mexomagno/TimerCharlas/Documentación/20131231_212455.jpg

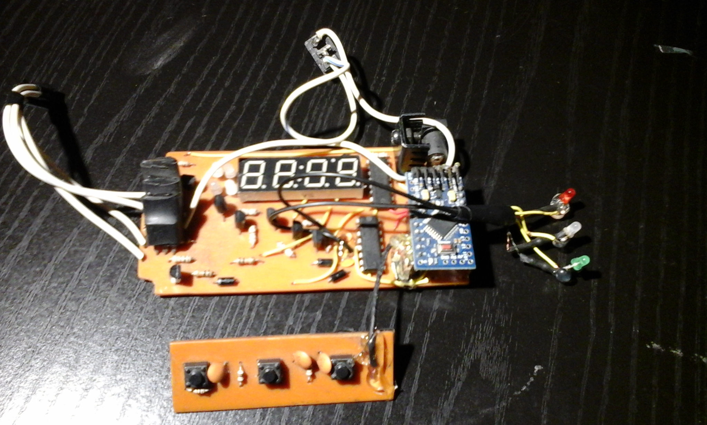
Documentación/20131231_212455.jpg
