mexomagno/TimerCharlas/Documentación/20131231_212502.jpg

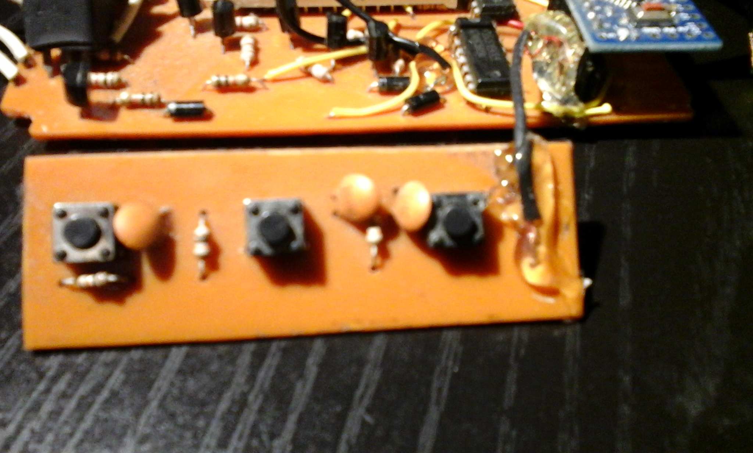
Documentación/20131231_212502.jpg
