mexomagno/TimerCharlas/Documentación/20131231_212513.jpg

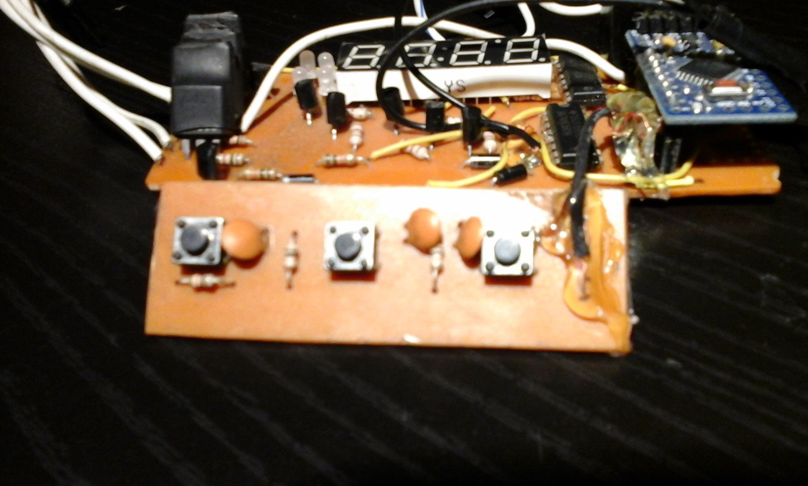
Documentación/20131231_212513.jpg
