mexomagno/TimerCharlas/Documentación/20131231_212531.jpg

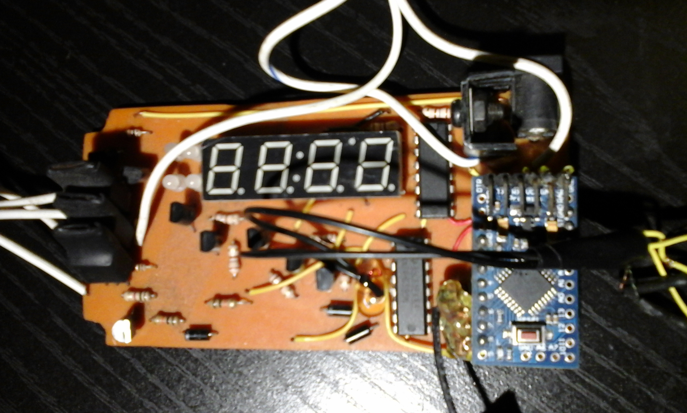
Documentación/20131231_212531.jpg
