mexomagno/TimerCharlas/Documentación/20131231_212555.jpg

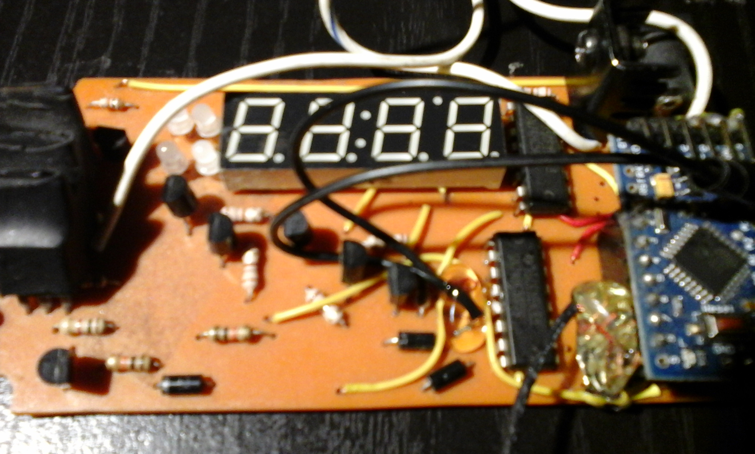
Documentación/20131231_212555.jpg
