mexomagno/TimerCharlas/Documentación/20131231_212558.jpg

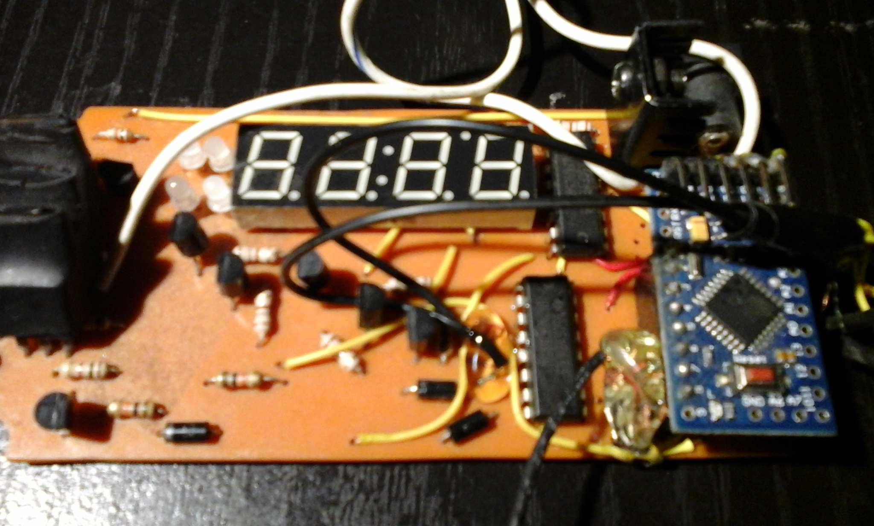
Documentación/20131231_212558.jpg
