mexomagno/TimerCharlas/Documentación/20131231_212613.jpg

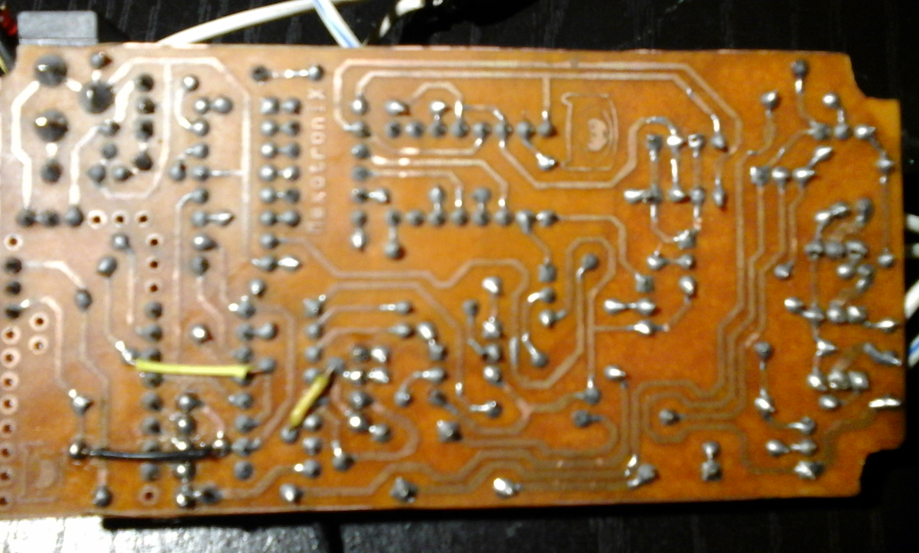
Documentación/20131231_212613.jpg
