mexomagno/TimerCharlas/Documentación/20131231_212618.jpg

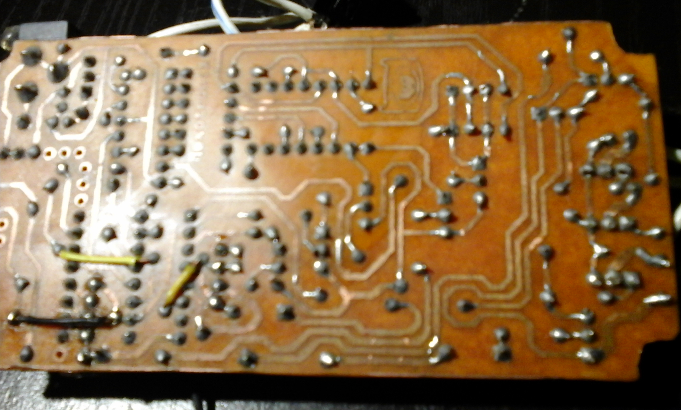
Documentación/20131231_212618.jpg
