mexomagno/TimerCharlas/Documentación/20131231_212626.jpg

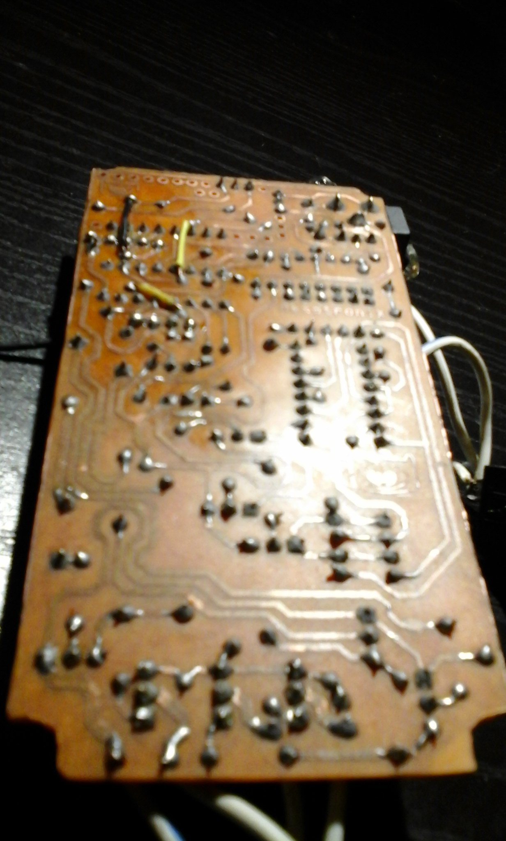
Documentación/20131231_212626.jpg
