mexomagno/TimerCharlas/Documentación/20131231_212638.jpg

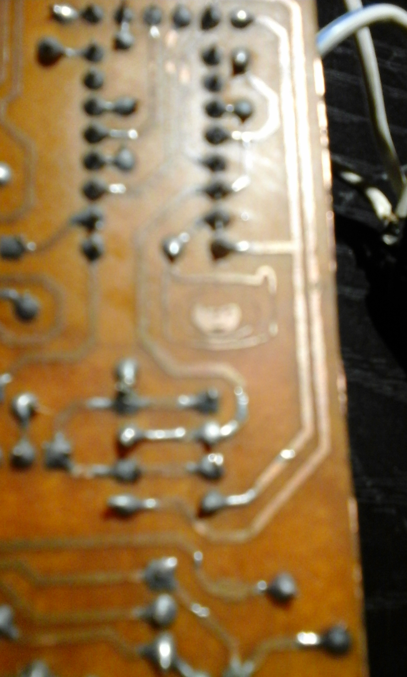
Documentación/20131231_212638.jpg
