mexomagno/TimerCharlas/Documentación/20131231_212643.jpg

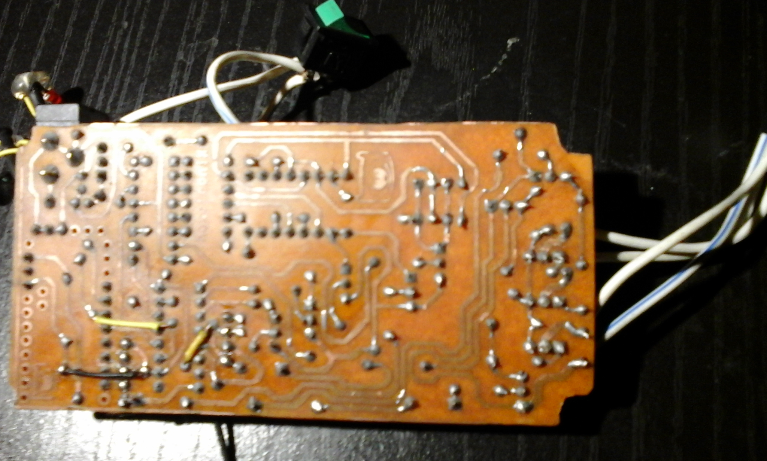
Documentación/20131231_212643.jpg
