mexomagno/TimerCharlas/Documentación/20131231_212644.jpg

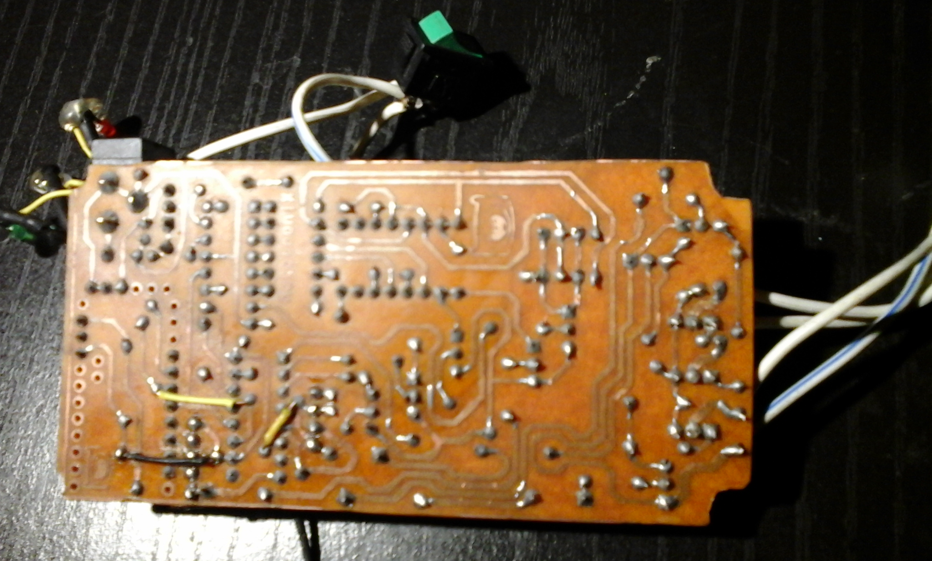
Documentación/20131231_212644.jpg
