mexomagno/TimerCharlas/Documentación/20131231_212645.jpg

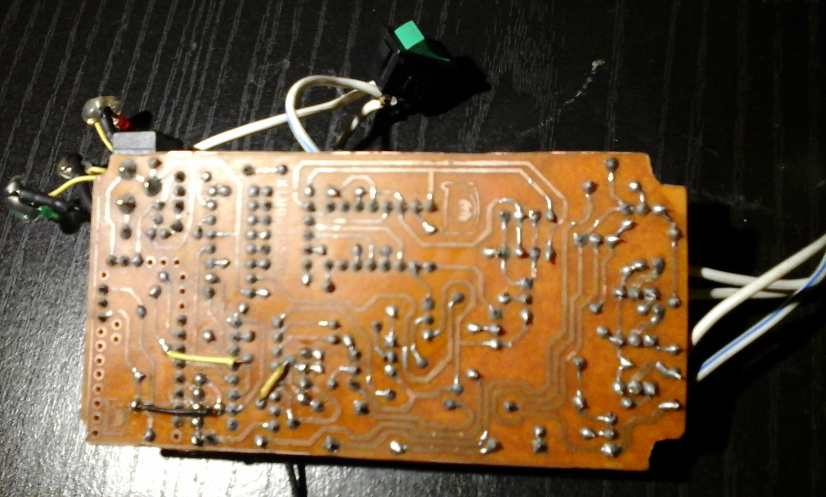
Documentación/20131231_212645.jpg
