mexomagno/TimerCharlas/Documentación/20131231_212648.jpg

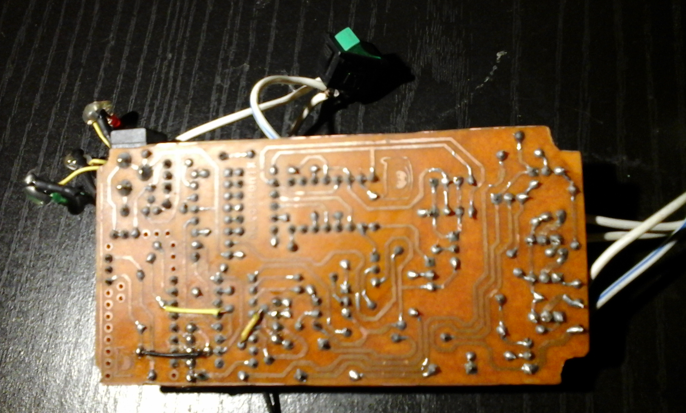
Documentación/20131231_212648.jpg
