mexomagno/TimerCharlas/Documentación/20131231_212739.jpg

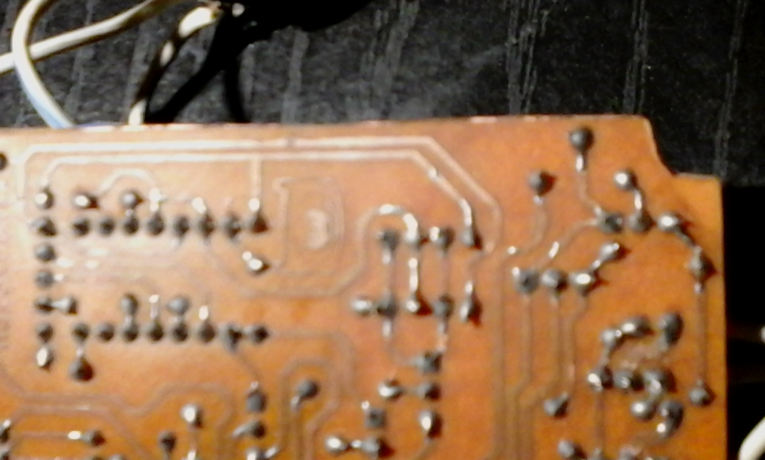
Documentación/20131231_212739.jpg
