mexomagno/TimerCharlas/Documentación/20131231_212742.jpg

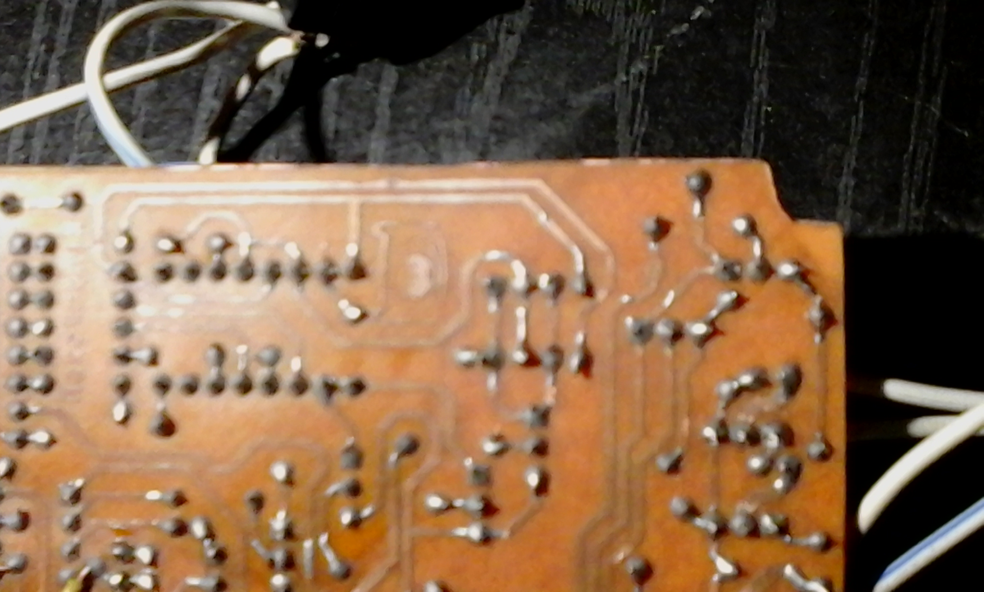
Documentación/20131231_212742.jpg
