mexomagno/TimerCharlas/Documentación/20131231_212754.jpg

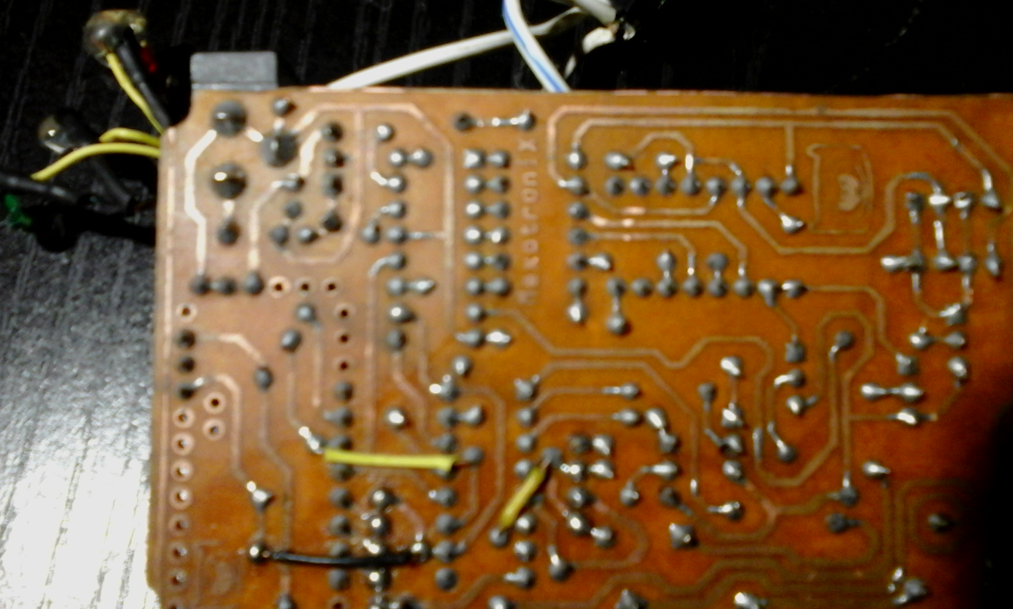
Documentación/20131231_212754.jpg
