mexomagno/TimerCharlas/Documentación/20131231_212808.jpg

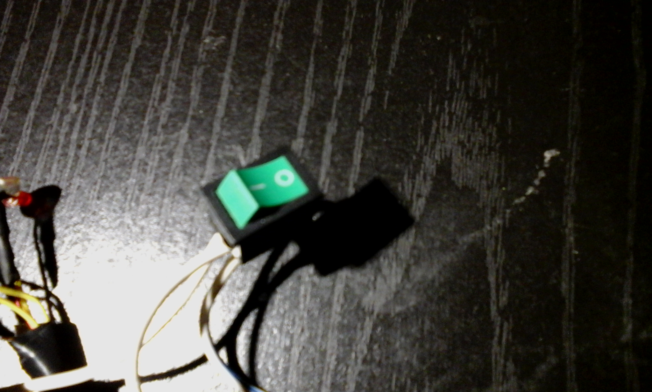
Documentación/20131231_212808.jpg
