mexomagno/TimerCharlas/Documentación/20131231_212821.jpg

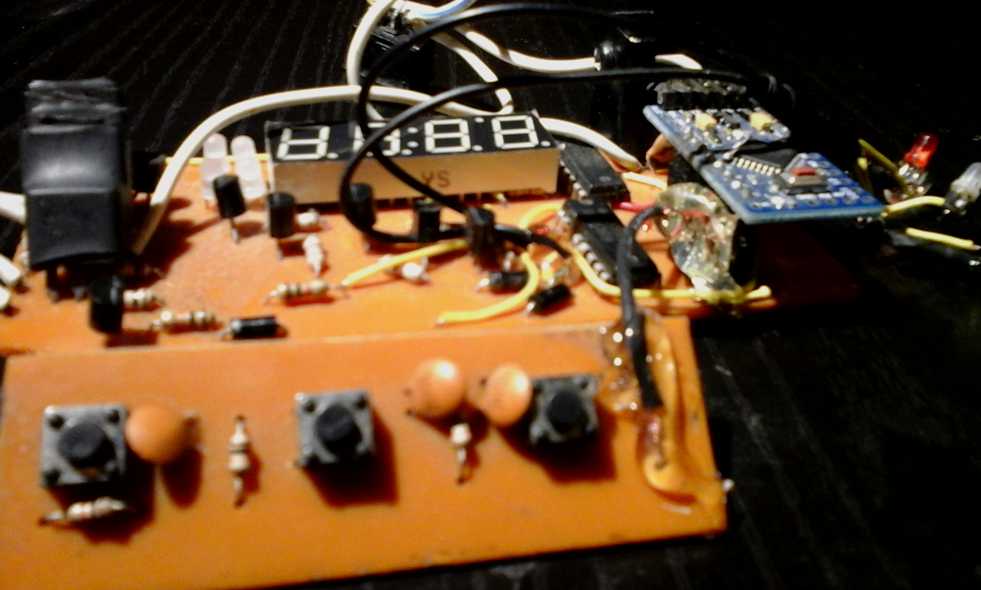
Documentación/20131231_212821.jpg
