mexomagno/TimerCharlas/Documentación/20131231_212827.jpg

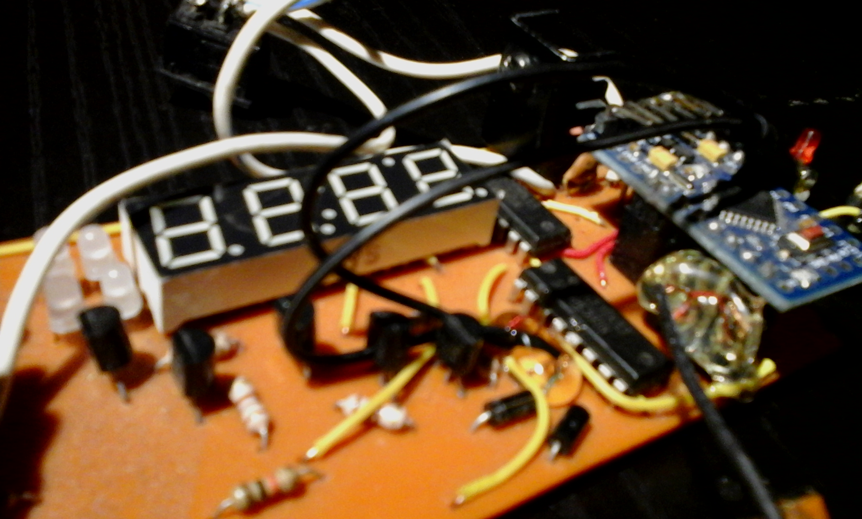
Documentación/20131231_212827.jpg
