mexomagno/TimerCharlas/Documentación/20131231_212839.jpg

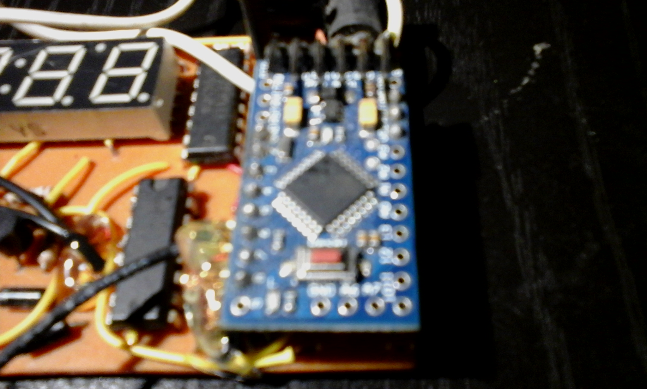
Documentación/20131231_212839.jpg
