mexomagno/TimerCharlas/Documentación/20131231_212845.jpg

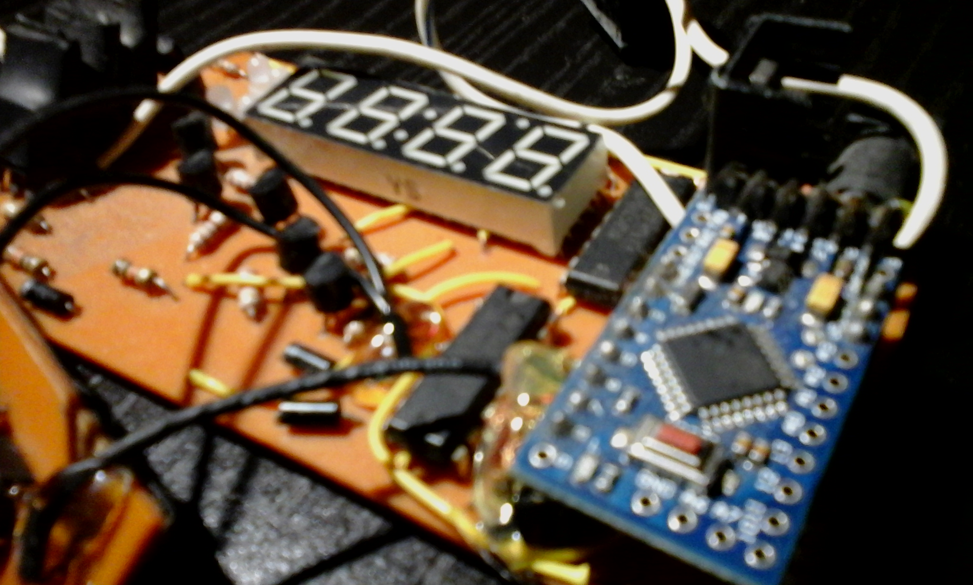
Documentación/20131231_212845.jpg
