mexomagno/TimerCharlas/Documentación/20131231_212901.jpg

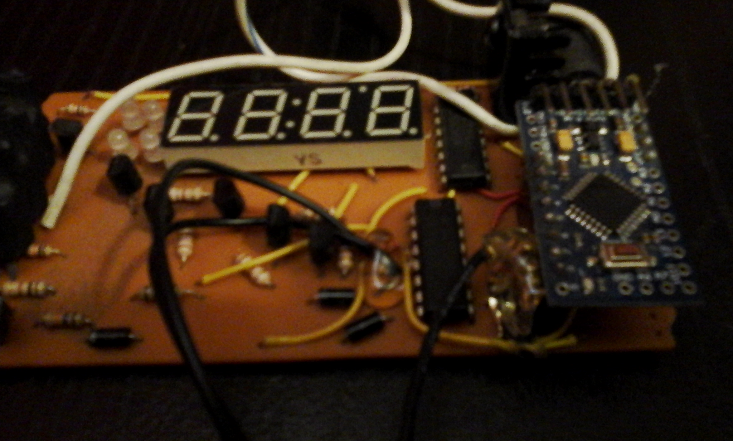
Documentación/20131231_212901.jpg
