mexomagno/TimerCharlas/Documentación/20131231_212908.jpg

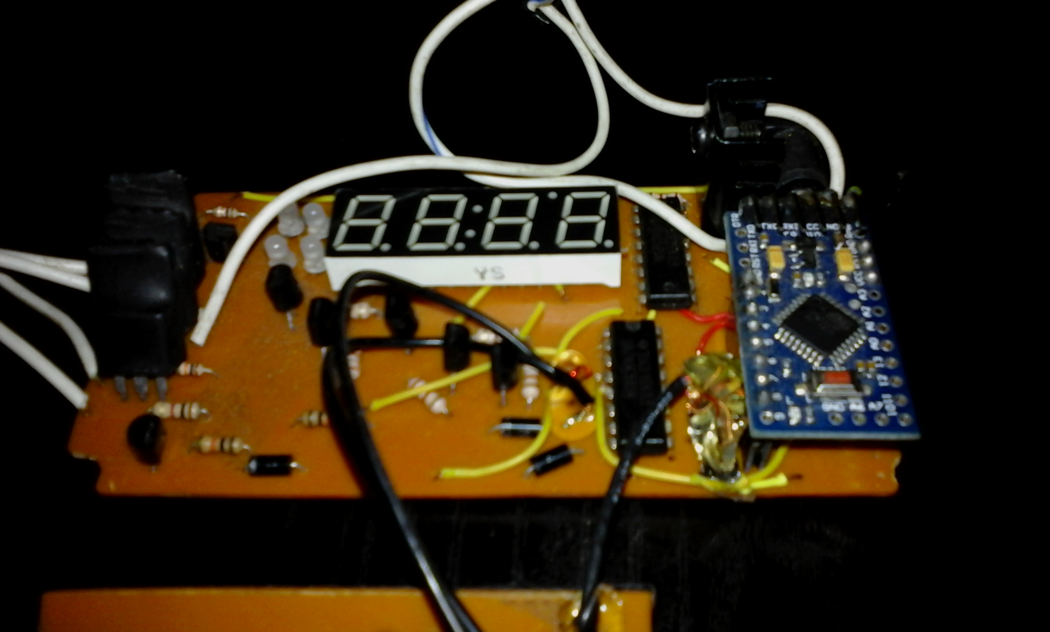
Documentación/20131231_212908.jpg
