mexomagno/TimerCharlas/Documentación/Produccion/primera iteración/IMG_20140923_220510.jpg

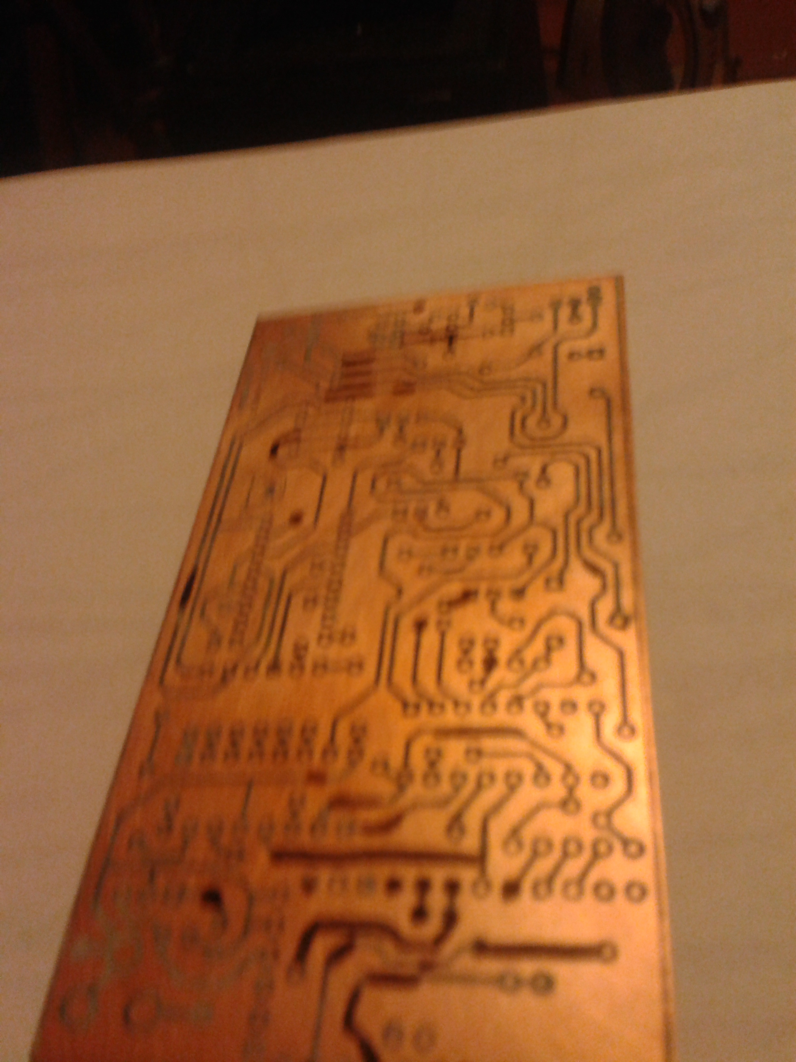
Documentación/Produccion/primera iteración/IMG_20140923_220510.jpg
