mexomagno/TimerCharlas/Documentación/Produccion/primera iteración/IMG_20140923_220513.jpg

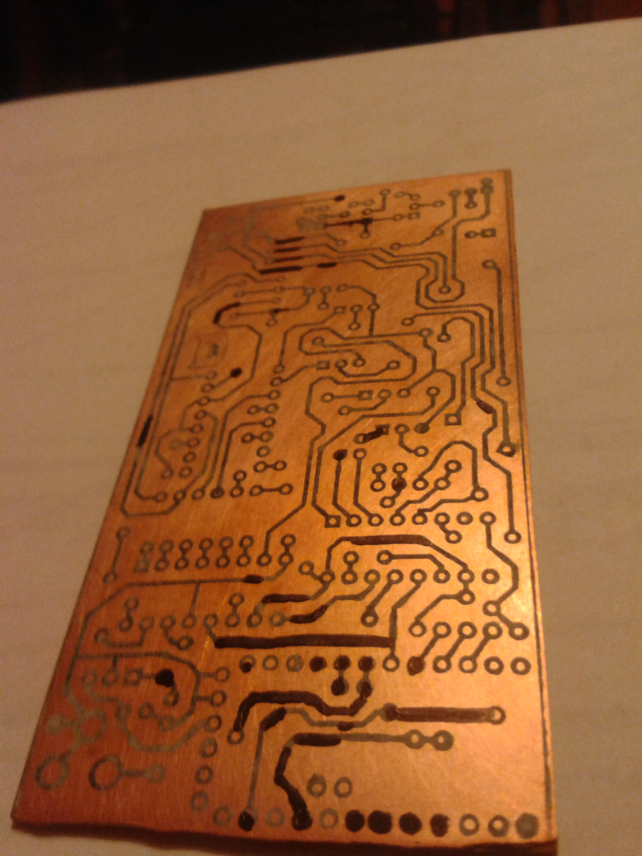
Documentación/Produccion/primera iteración/IMG_20140923_220513.jpg
