mexomagno/TimerCharlas/Documentación/Produccion/primera iteración/IMG_20140923_220547.jpg

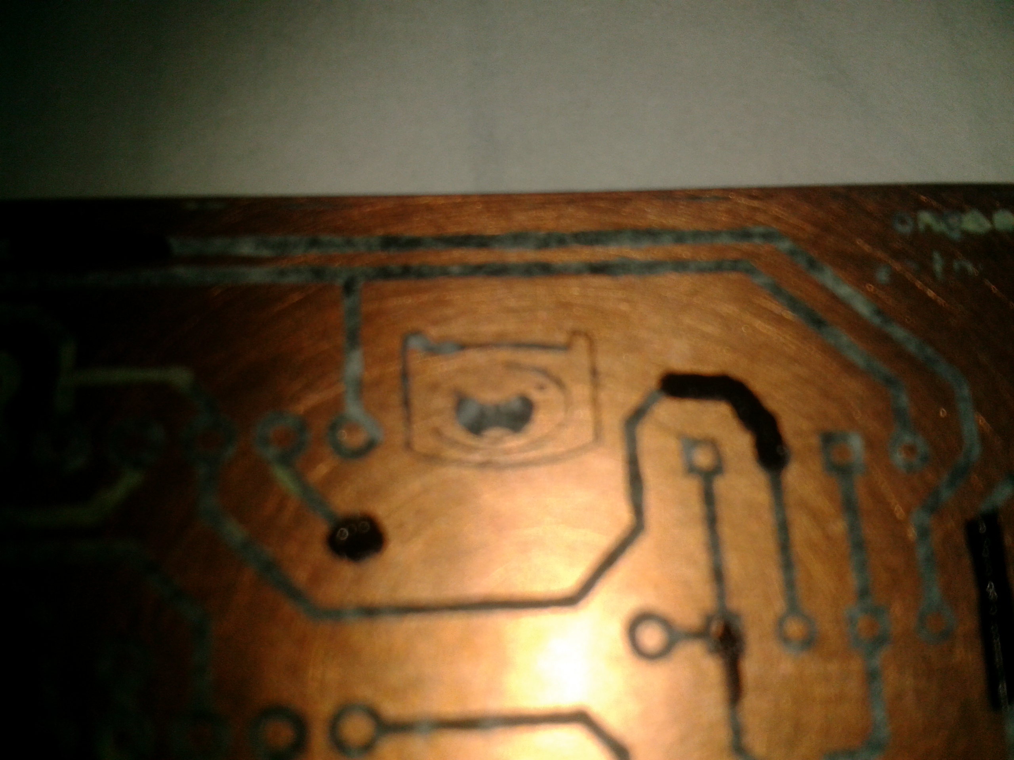
Documentación/Produccion/primera iteración/IMG_20140923_220547.jpg
