mexomagno/TimerCharlas/Documentación/Produccion/primera iteración/IMG_20140923_220606.jpg

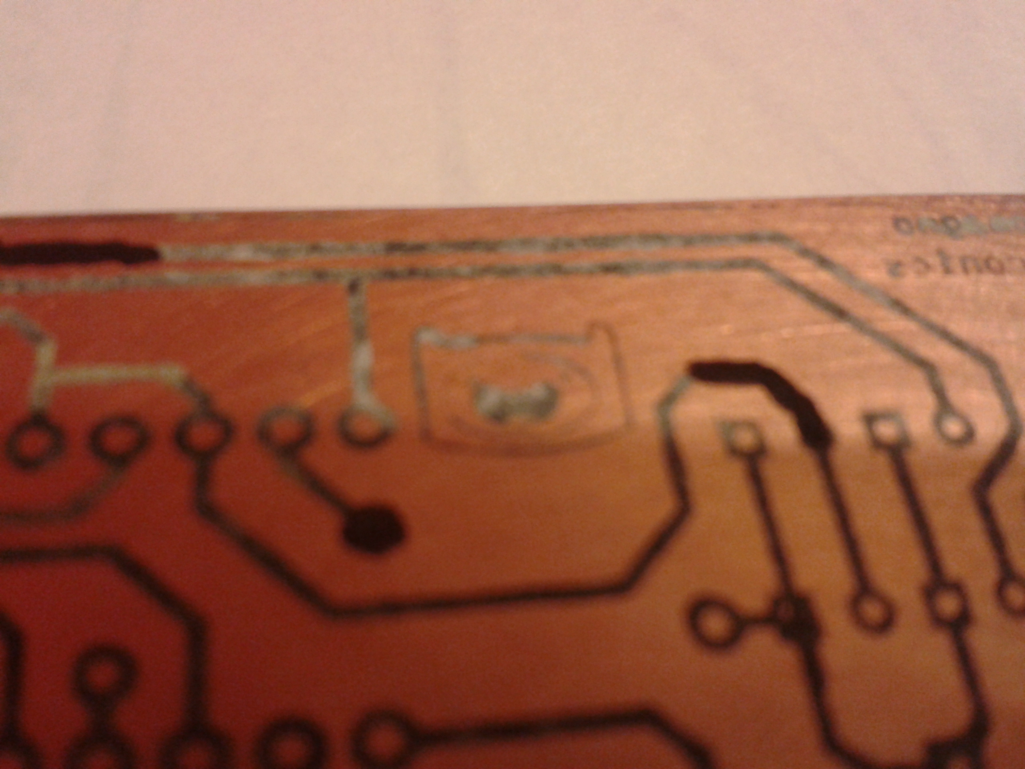
Documentación/Produccion/primera iteración/IMG_20140923_220606.jpg
