mexomagno/TimerCharlas/Documentación/Produccion/primera iteración/IMG_20140923_230915.jpg

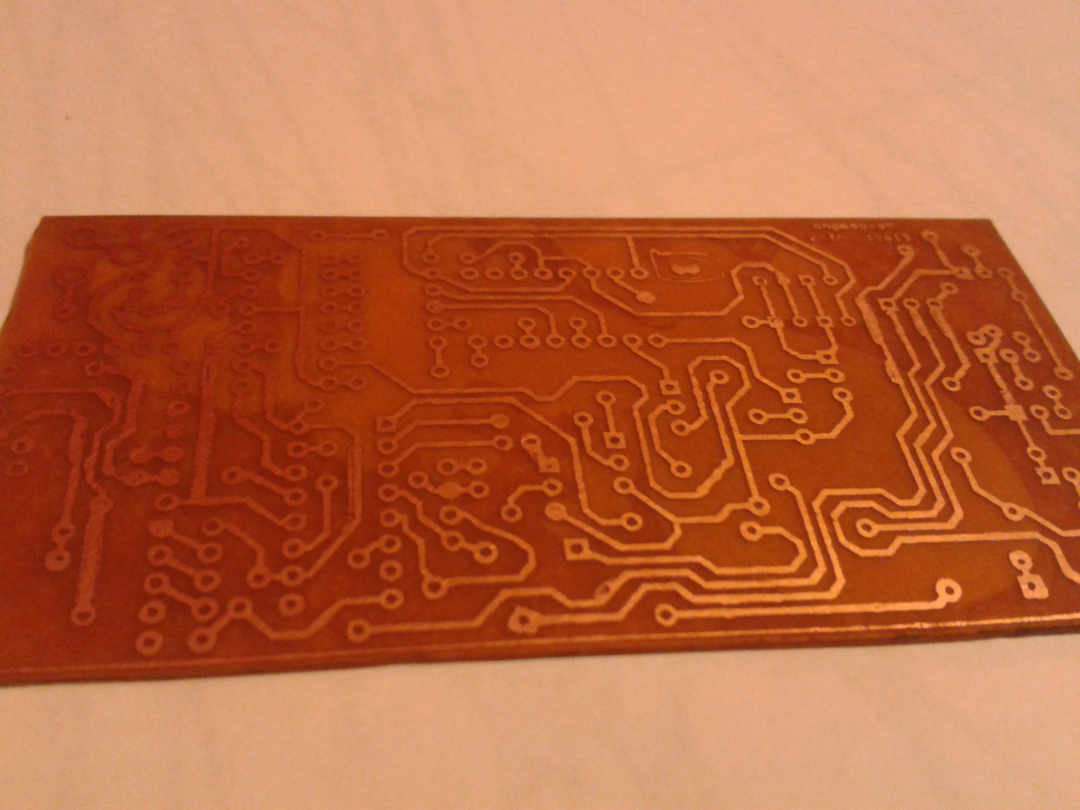
Documentación/Produccion/primera iteración/IMG_20140923_230915.jpg
