mexomagno/TimerCharlas/Documentación/Produccion/primera iteración/IMG_20140923_230923.jpg

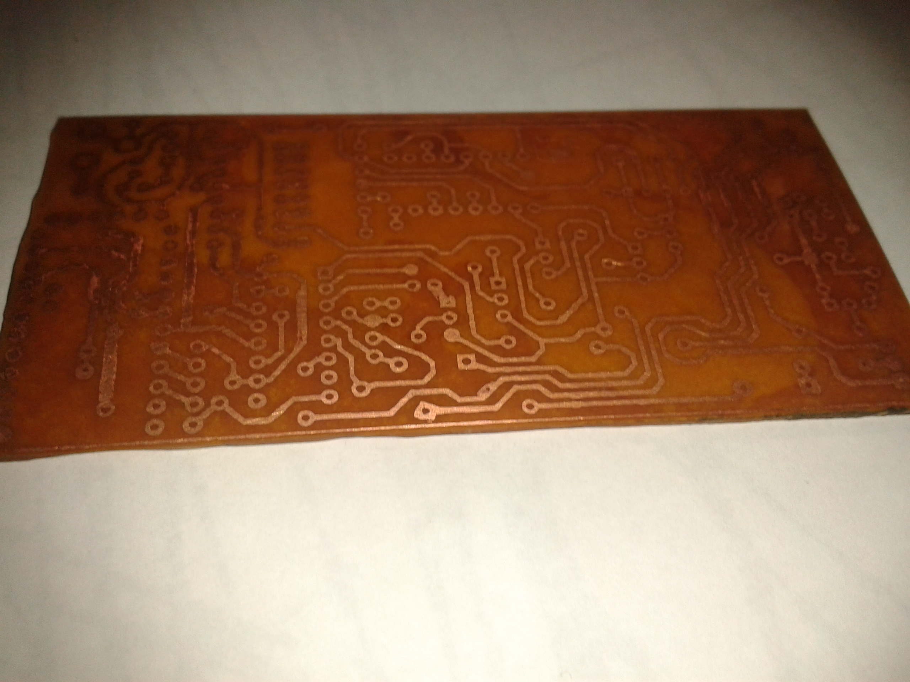
Documentación/Produccion/primera iteración/IMG_20140923_230923.jpg
