mexomagno/TimerCharlas/Documentación/Produccion/primera iteración/IMG_20140923_230930.jpg

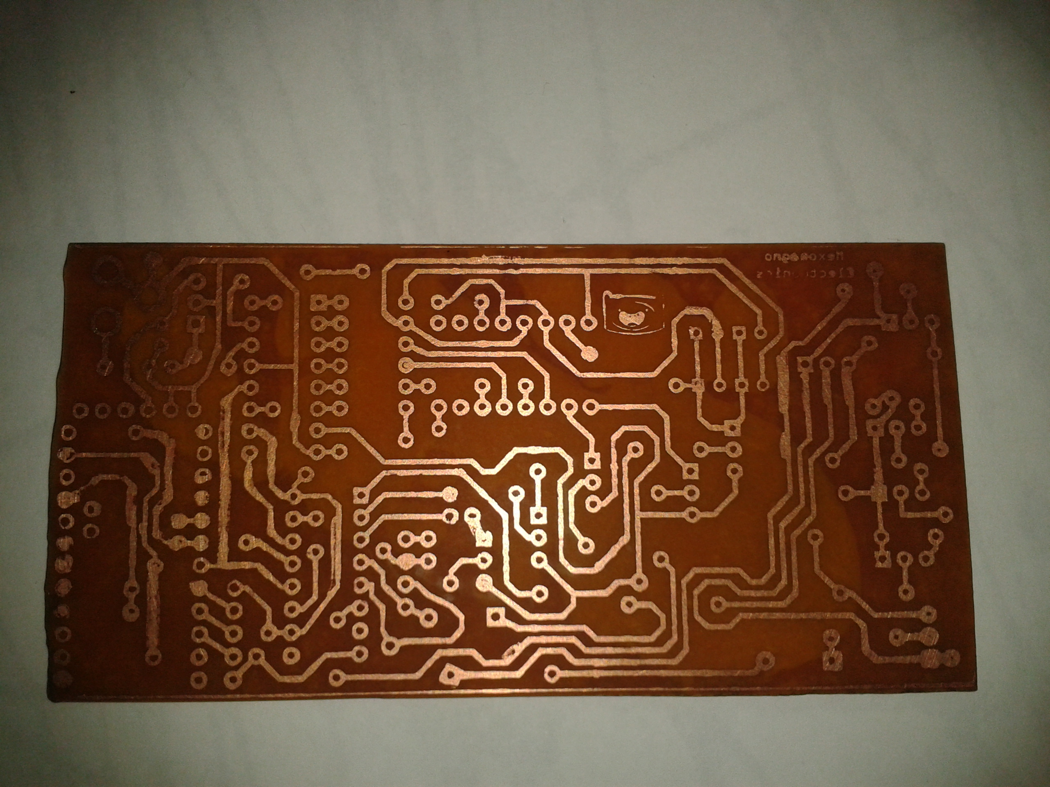
Documentación/Produccion/primera iteración/IMG_20140923_230930.jpg
