mexomagno/TimerCharlas/Documentación/Produccion/primera iteración/IMG_20140925_010022.jpg

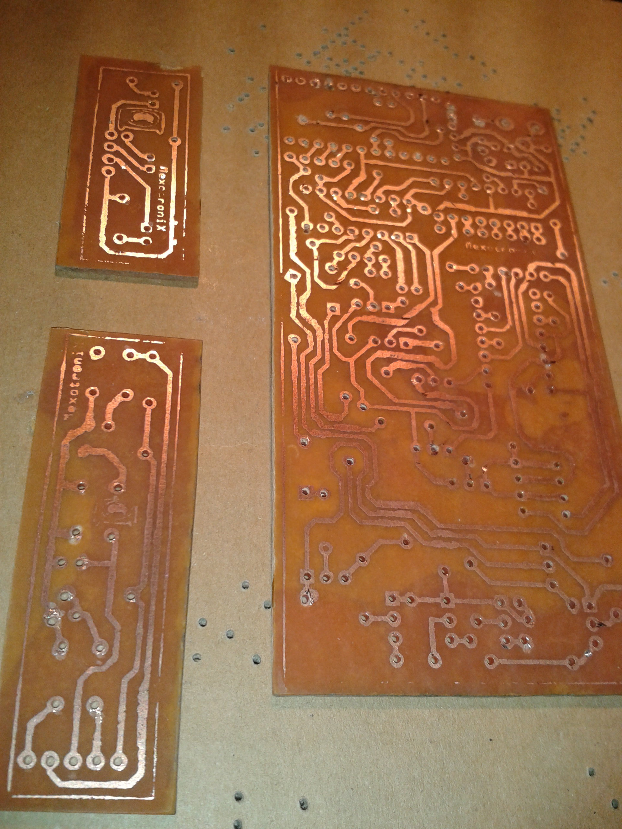
Documentación/Produccion/primera iteración/IMG_20140925_010022.jpg
