mexomagno/TimerCharlas/Documentación/Produccion/primera iteración/IMG_20140925_010057.jpg

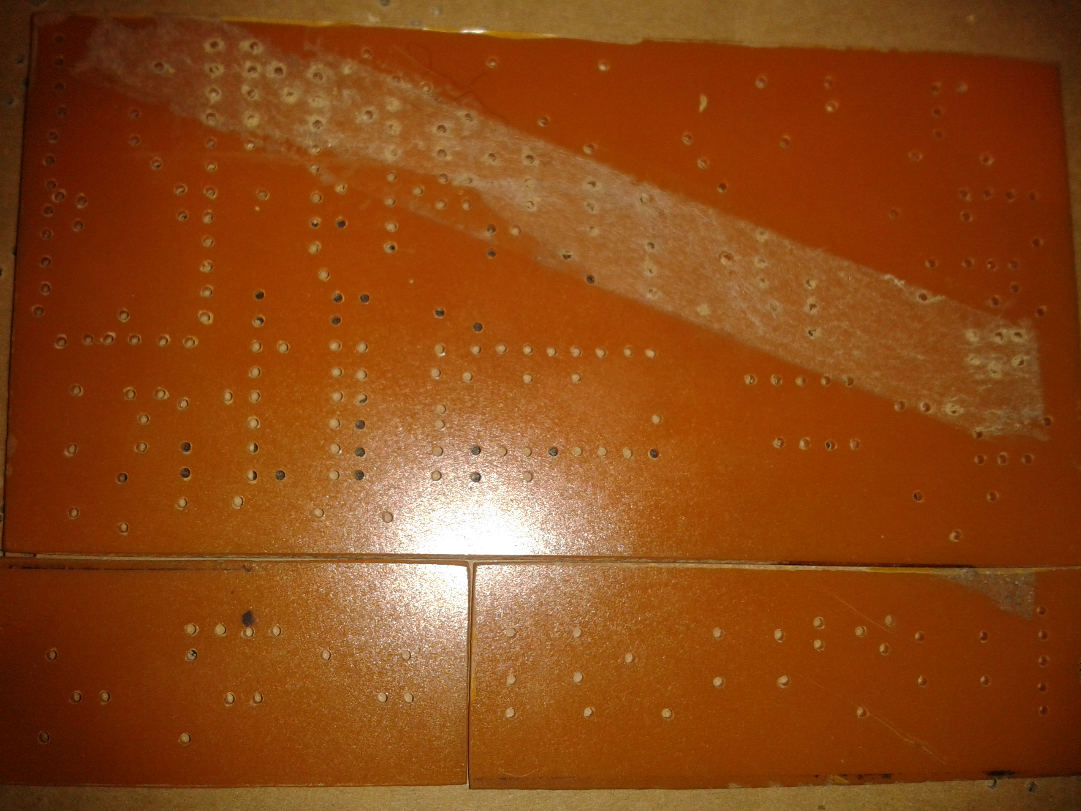
Documentación/Produccion/primera iteración/IMG_20140925_010057.jpg
