mexomagno/TimerCharlas/Documentación/Produccion/primera iteración/IMG_20140925_010109.jpg

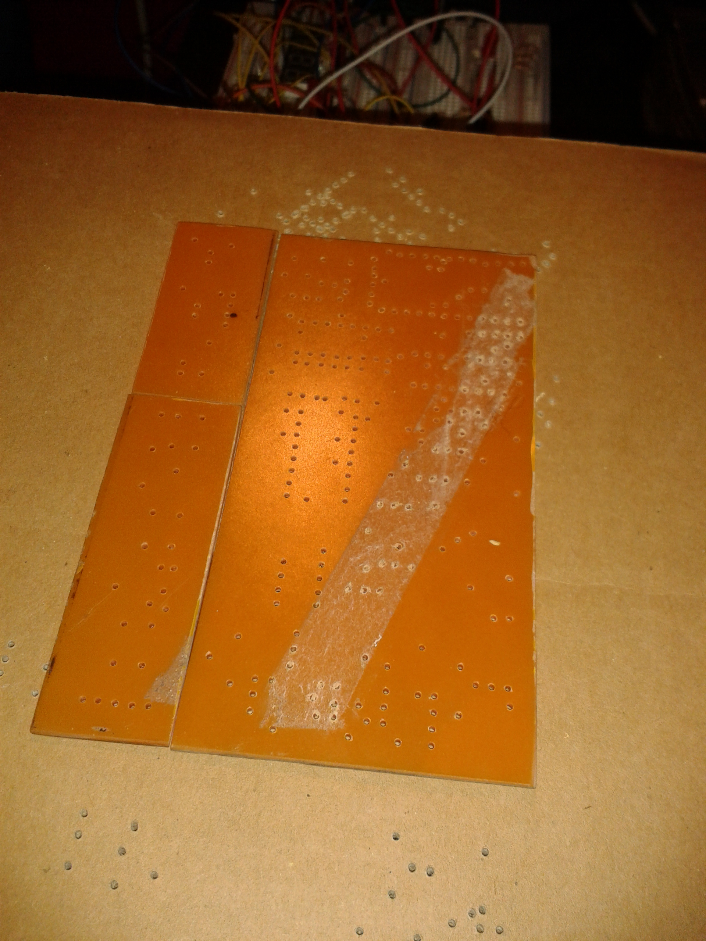
Documentación/Produccion/primera iteración/IMG_20140925_010109.jpg
