mexomagno/TimerCharlas/Documentación/Produccion/primera iteración/IMG_20140925_025734.jpg

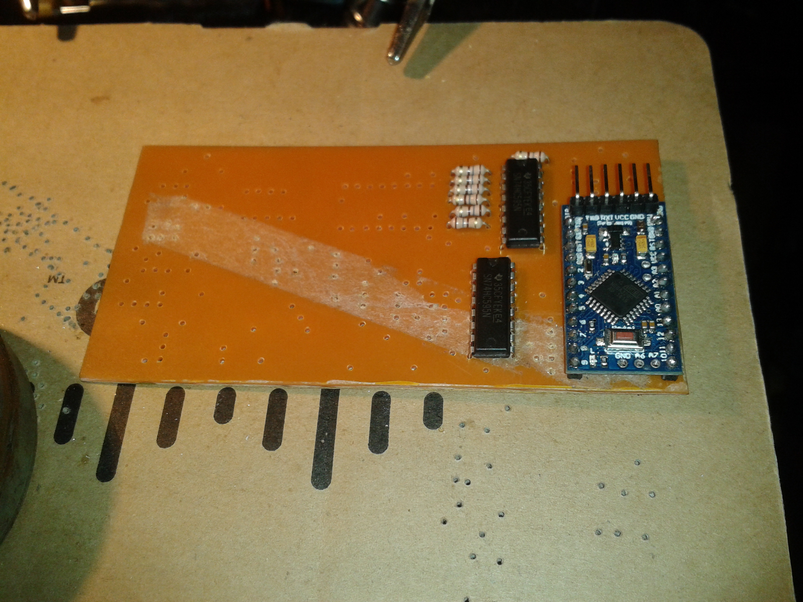
Documentación/Produccion/primera iteración/IMG_20140925_025734.jpg
