mexomagno/TimerCharlas/Documentación/Produccion/primera iteración/IMG_20140925_025738.jpg

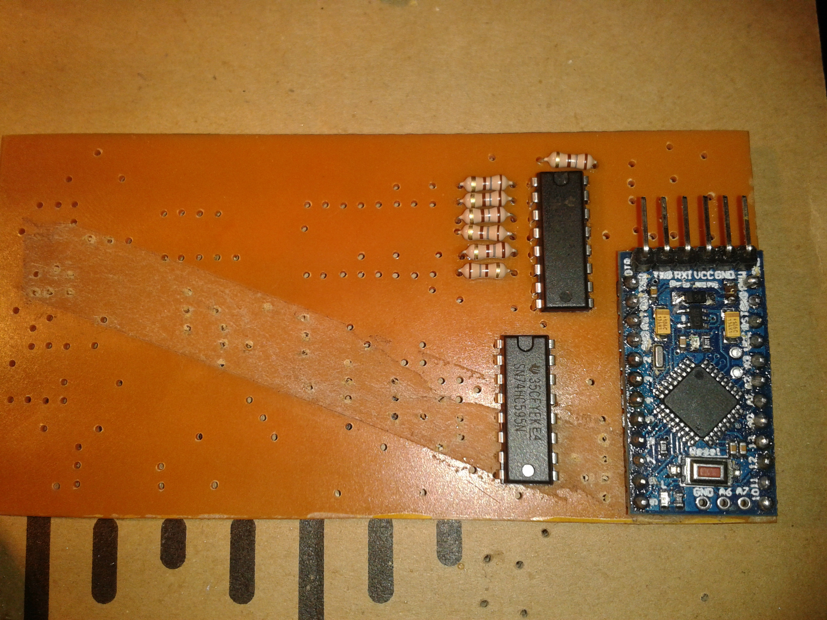
Documentación/Produccion/primera iteración/IMG_20140925_025738.jpg
