mexomagno/TimerCharlas/Documentación/Produccion/primera iteración/IMG_20140927_193842.jpg

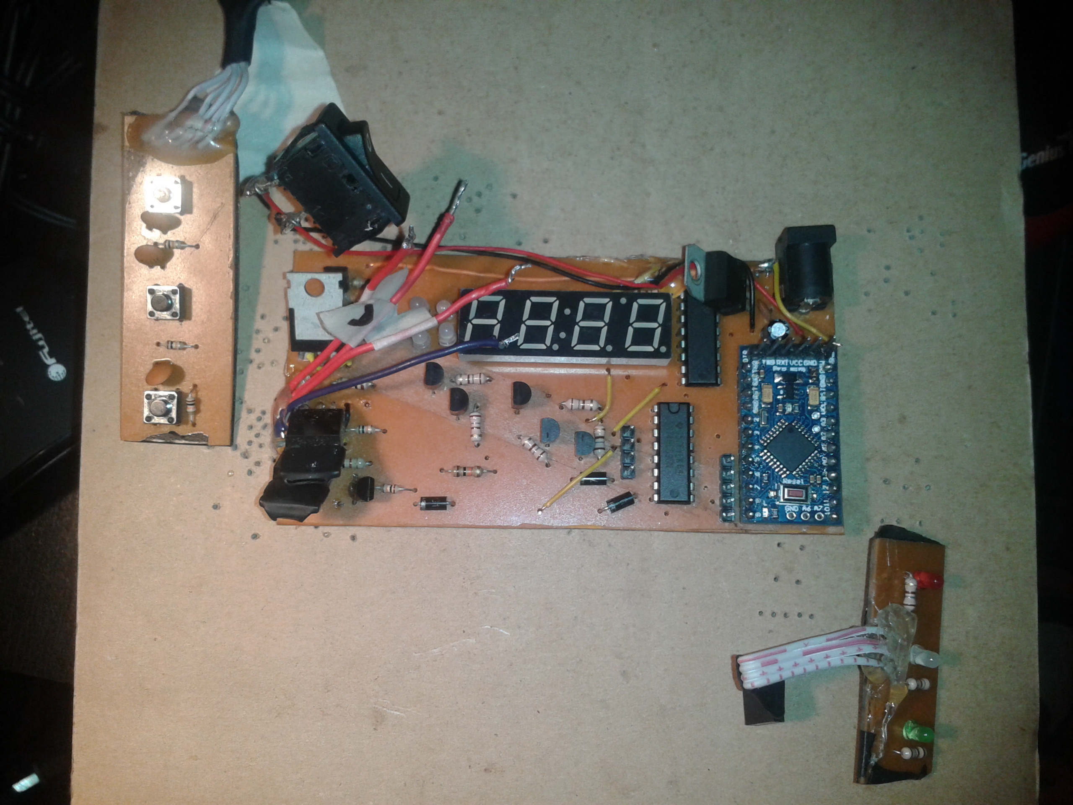
Documentación/Produccion/primera iteración/IMG_20140927_193842.jpg
