mexomagno/TimerCharlas/Documentación/Produccion/primera iteración/IMG_20140927_193904.jpg

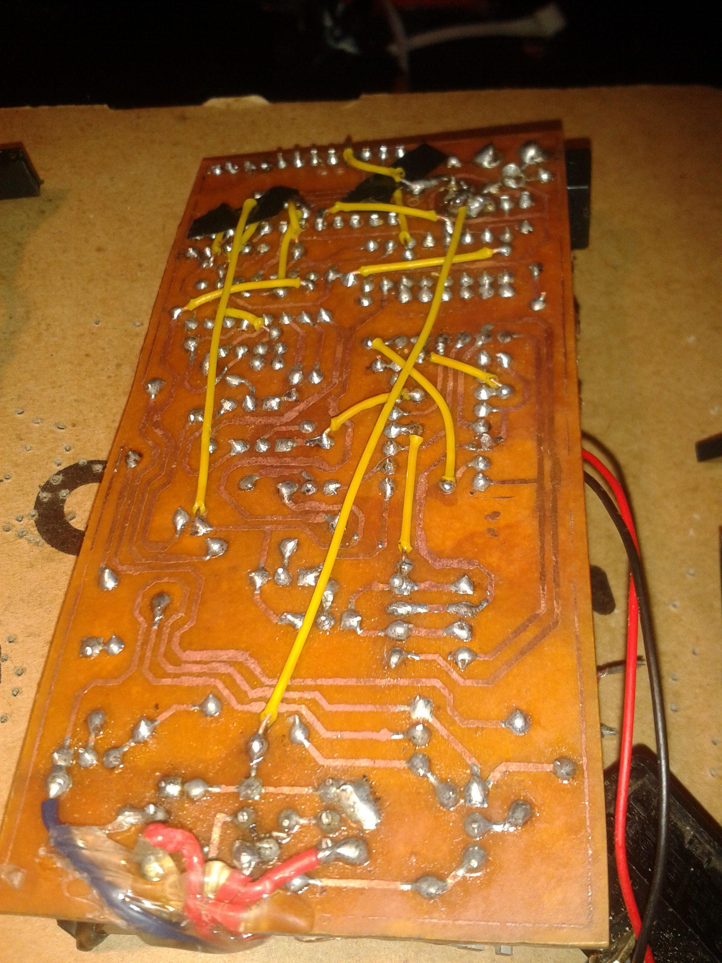
Documentación/Produccion/primera iteración/IMG_20140927_193904.jpg
