mexomagno/TimerCharlas/Documentación/Produccion/Segunda iteración/IMG_20141004_144702.jpg

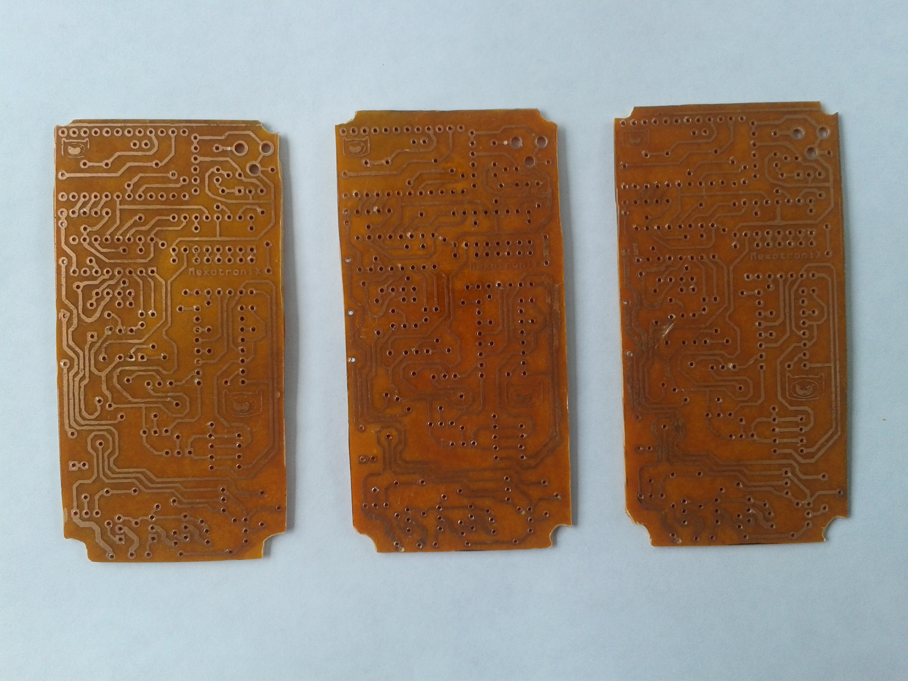
Documentación/Produccion/Segunda iteración/IMG_20141004_144702.jpg
