mexomagno/TimerCharlas/Documentación/Produccion/Segunda iteración/IMG_20141004_144715.jpg

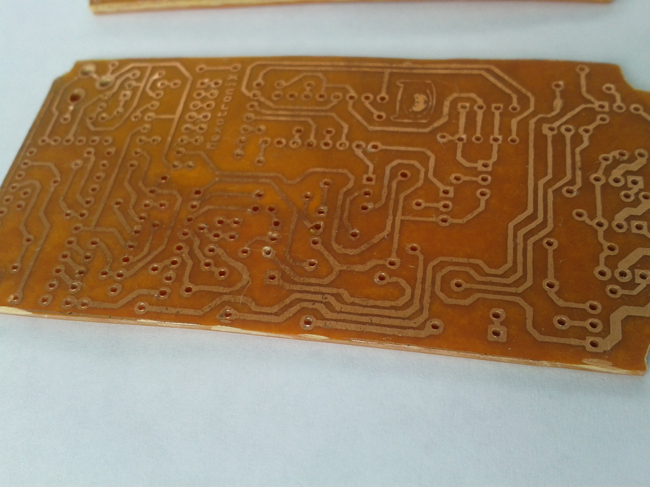
Documentación/Produccion/Segunda iteración/IMG_20141004_144715.jpg
