mexomagno/TimerCharlas/Documentación/Produccion/Segunda iteración/IMG_20141004_144727.jpg

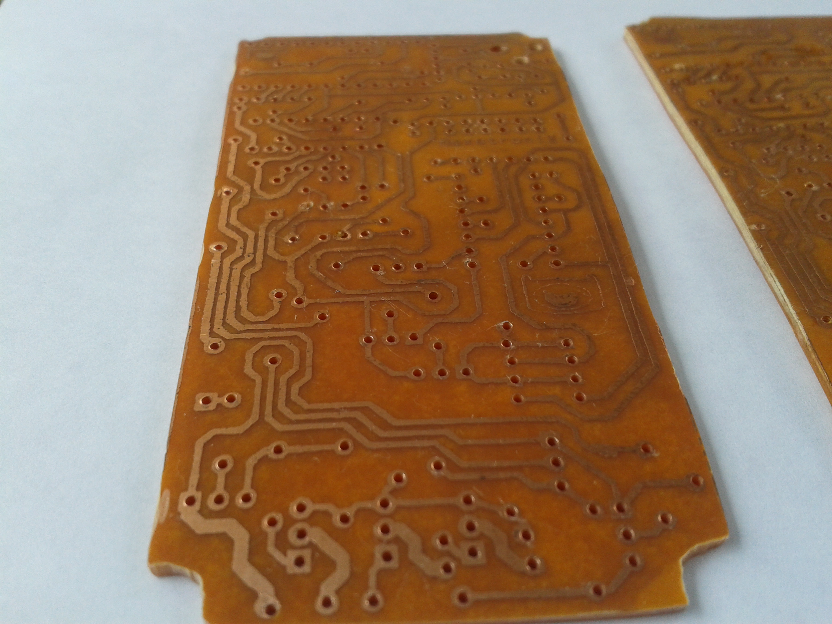
Documentación/Produccion/Segunda iteración/IMG_20141004_144727.jpg
