mexomagno/TimerCharlas/Prototipo/prototipo1 colores.png

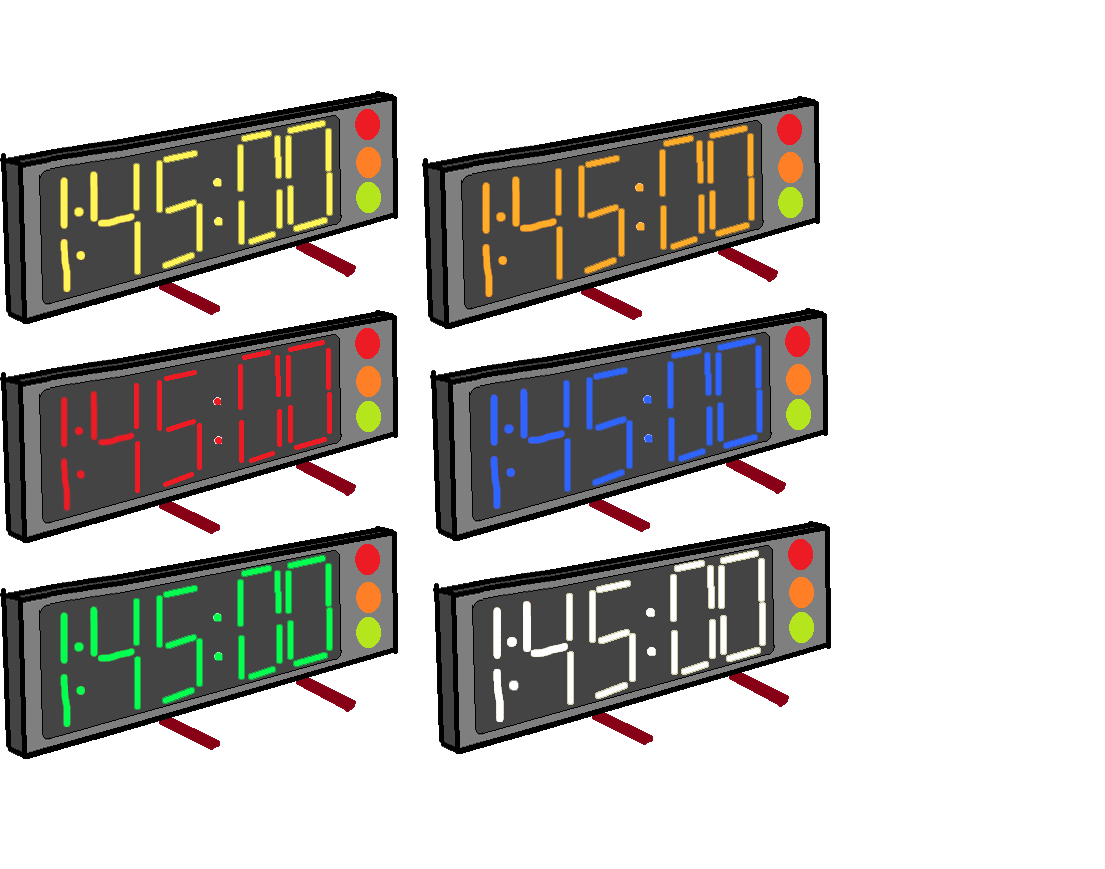
Prototipo/prototipo1 colores.png
