mexomagno/TimerCharlas/Prototipo/prototipo1.png

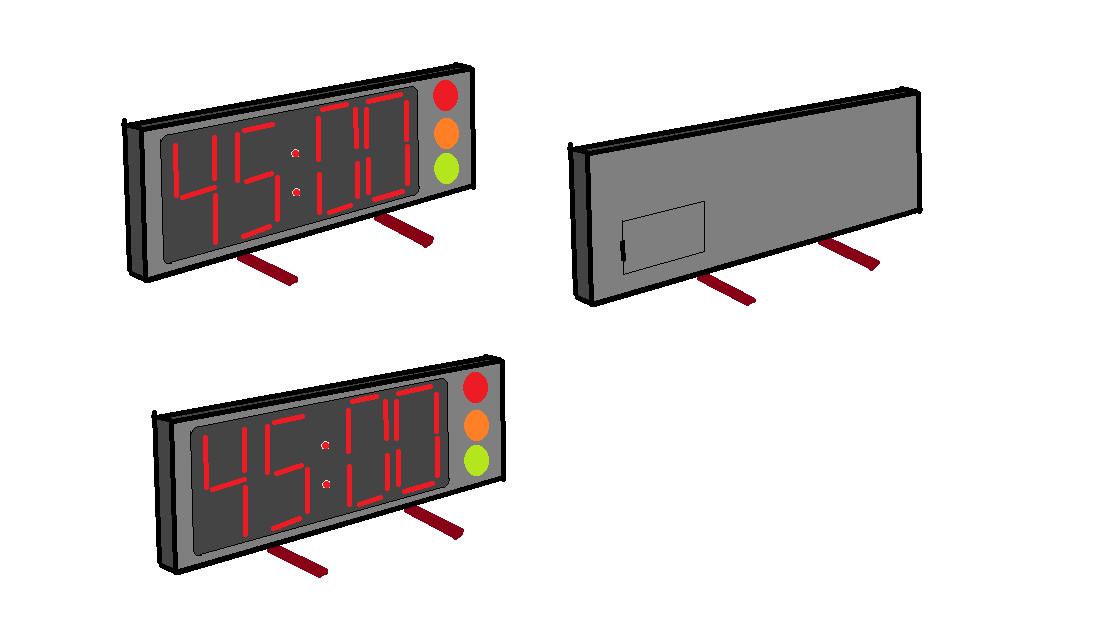
Prototipo/prototipo1.png
