mexomagno/TimerCharlas/Hardware/Componentes/camera/IMG_20140820_161452.jpg

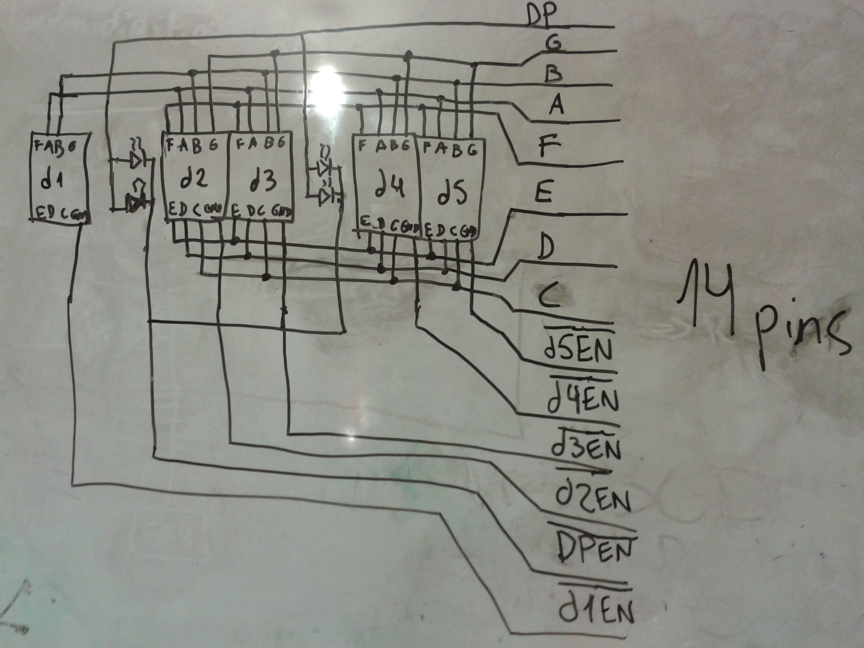
Hardware/Componentes/camera/IMG_20140820_161452.jpg
