mexomagno/TimerCharlas/Hardware/Componentes/camera/IMG_20140820_162958.jpg

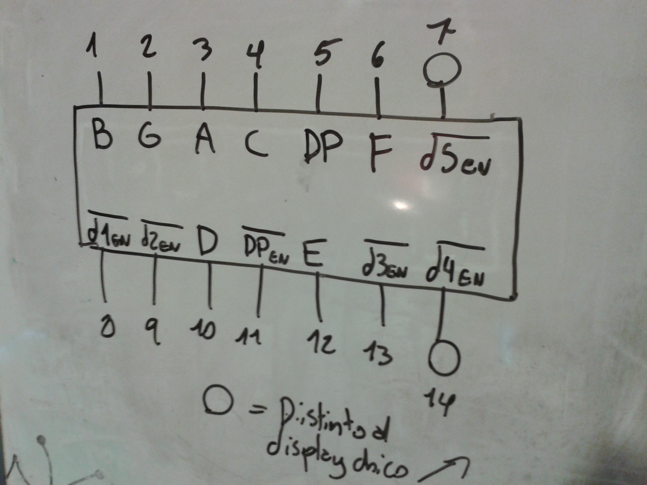
Hardware/Componentes/camera/IMG_20140820_162958.jpg
