mexomagno/TimerCharlas/Hardware/Componentes/camera/IMG_20140820_182516.jpg

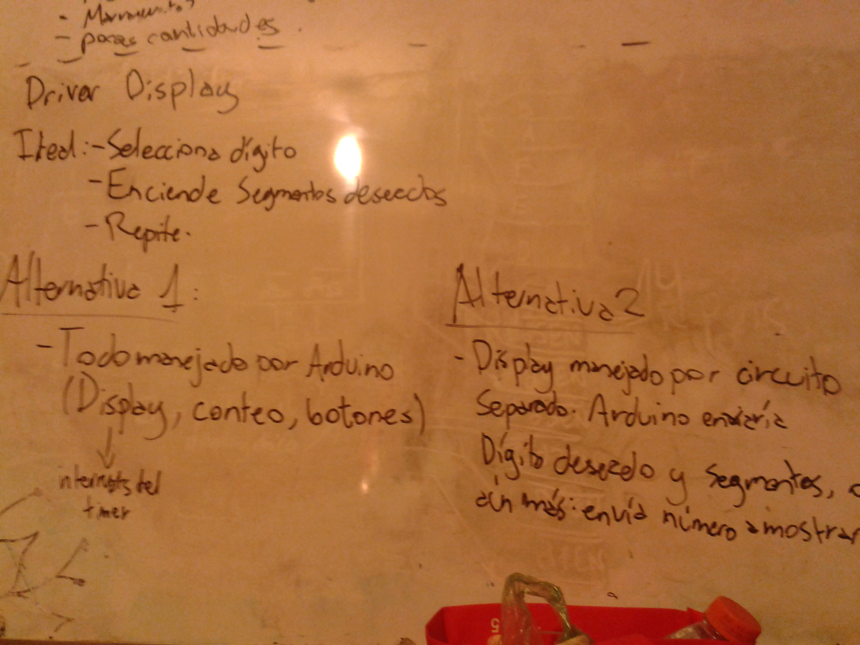
Hardware/Componentes/camera/IMG_20140820_182516.jpg
