mexomagno/TimerCharlas/Hardware/Componentes/camera/IMG_20140820_191519.jpg

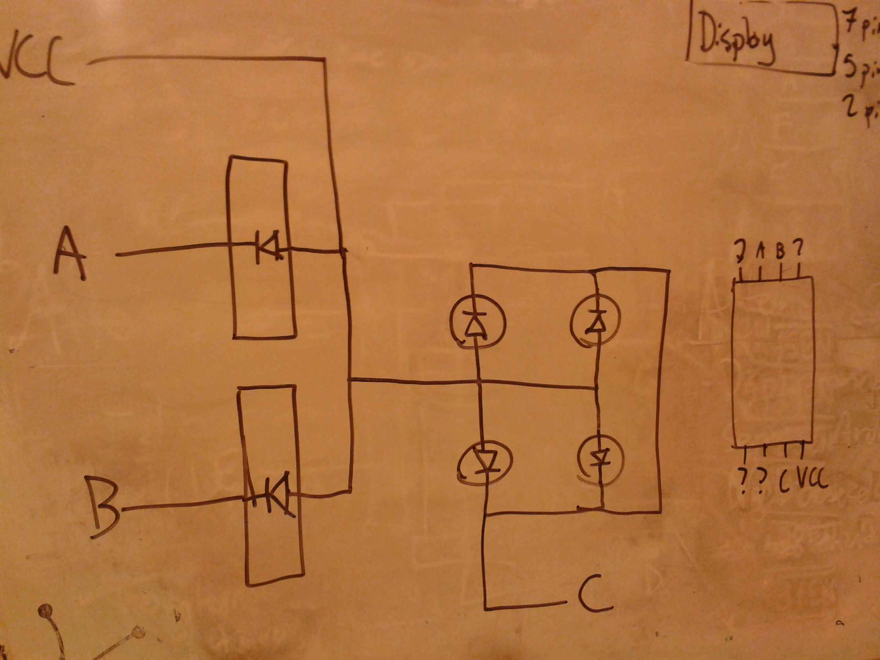
Hardware/Componentes/camera/IMG_20140820_191519.jpg
