mexomagno/TimerCharlas/Hardware/Componentes/camera/IMG_20140820_192302.jpg

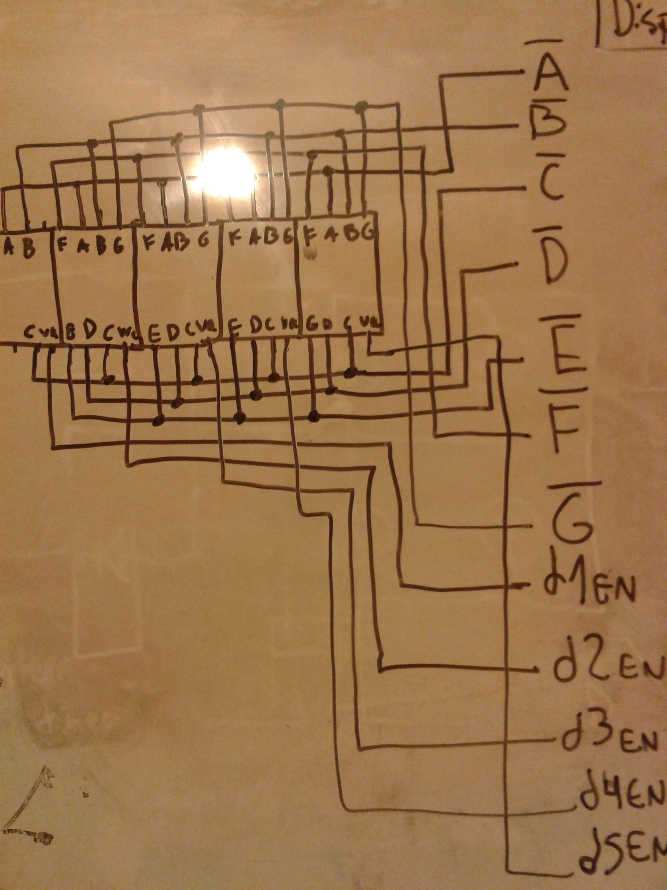
Hardware/Componentes/camera/IMG_20140820_192302.jpg
