mexomagno/TimerCharlas/Hardware/Componentes/camera/IMG_20140820_192306.jpg

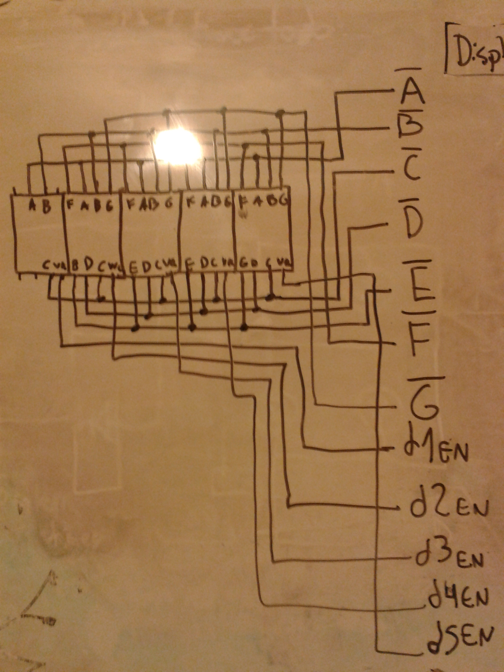
Hardware/Componentes/camera/IMG_20140820_192306.jpg
