mexomagno/TimerCharlas/Documentación/Proto test count/IMG_20140827_024634.jpg

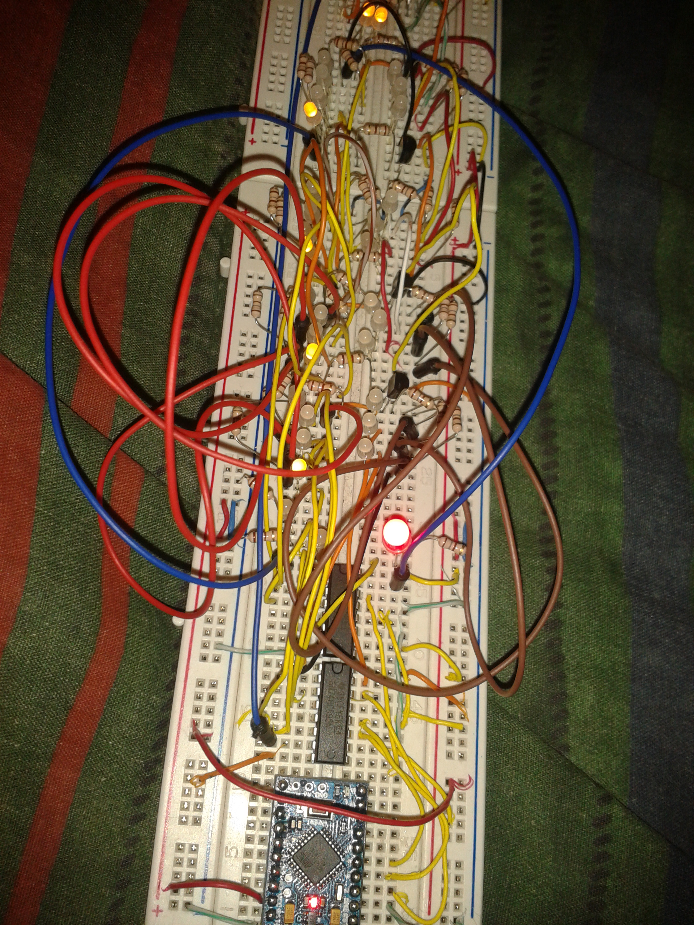
Documentación/Proto test count/IMG_20140827_024634.jpg
