mexomagno/TimerCharlas/Documentación/Proto test count/IMG_20140827_024645.jpg

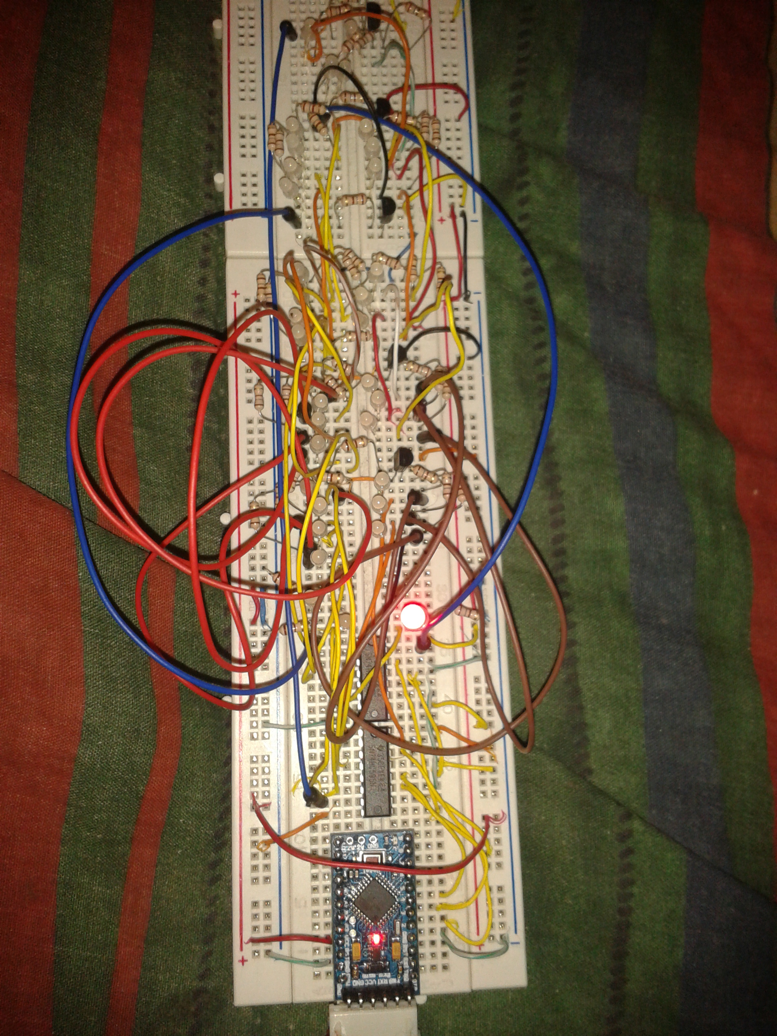
Documentación/Proto test count/IMG_20140827_024645.jpg
