mexomagno/TimerCharlas/Hardware/Componentes/ltSpice/Display 7 segmentos ESPECIAL.asc

D1: LED
D2: LED
D3: LED
D4: LED
D26: LED
D27: LED
D28: LED
D29: LED
D30: LED
D31: LED
D32: LED
D33: LED
D34: LED
D35: LED
R1: res; 165; tol=5 pwr=1/4
R2: res; 165; tol=5 pwr=1/4
R3: res; 165; tol=5 pwr=1/4
R4: res; 165; tol=5 pwr=1/4
R16: res; 165; tol=5 pwr=1/4
R17: res; 165; tol=5 pwr=1/4
R18: res; 165; tol=5 pwr=1/4
R19: res; 165; tol=5 pwr=1/4
R20: res; 165; tol=5 pwr=1/4
R21: res; 165; tol=5 pwr=1/4
R22: res; 165; tol=5 pwr=1/4
R23: res; 165; tol=5 pwr=1/4
R24: res; 165; tol=5 pwr=1/4
R25: res; 165; tol=5 pwr=1/4
Named nets: 5V, A, B, C, D, E, F, G
Led ROJO: 1.7v, funciona a 20mA.
Resistencia en serie con cada uno.
Diseñado para funcionar con 5V
(5-1.7)/0.02=165 ohms cada resistencia.
 
Las resistencias reales son de 180 ohms
