mexomagno/TimerCharlas/Hardware/Componentes/ltSpice/Timer completo.asc

C1: cap; 10µ; V=100
C2: cap; 1µ
Luz_Amarilla: LED
Luz_Roja: LED
Luz_Verde: LED
Q1: npn
Q2: npn
Q3: npn
Q4: npn
Q5: npn
R1: res; 180; tol=5 pwr=0.25
R2: res; 180; tol=5 pwr=0.25
R3: res; 180; tol=5 pwr=0.25
R4: res; 180; tol=5 pwr=0.25
R5: res; 180; tol=5 pwr=0.25
R6: res; 180; tol=5 pwr=0.25
R7: res; 180; tol=5 pwr=0.25
R8: res; 180; tol=5 pwr=0.25
U1: 7805
V1: voltage; 9
X1: 
X2: 
X3: 
X4: ULN2003
Named nets: PIN2, PIN3, PIN4, 0, PIN5V
Display tiene resistencias internas.
Alimentar display directamente.
 
SEGMENTOS (A B C D E F G):
-Pueden entregar máximo 100mA. Fácilmente manejados por ULN2003.
DIGITOS (d1 d2 d3 d4 d5):
-Pueden consumir máximo 700mA (7 segmentos encendidos a la vez).
-Shift register no puede suplir esta corriente.
-Solución: Usar transistores.
 
TRANSISTOR:
-PN2222A: Colector hecho para 500mA
-Solución: poner 2 en paralelo
 
Poniendo como límite que pasen 800mA por cada dX:
-Cada par de transistores en paralelo pasará 800mA.
-Cada transistor debe pasar 400mA.
-Resistencias dependen del valor del LOAD de los leds
 
Modificación: un solo transistor por dígito. transistor BC337 parece que aguanta :D
