mexomagno/TimerCharlas/Hardware/Componentes/ltSpice/Display 5 dígitos.asc

X1: 
X2: 
X3: 
X4: 
X5: 
Named nets: ~A, ~B, ~C, ~D, ~E, ~F, ~G, d1, d2, d3, d4, d5
A lo más 1 sólo dX puede estar prendido.
Por cada segmento ~X (A B C D E F G) salen máximo 100mA (5 leds cada uno).
Por cada selector de dígito dX (1 2 3 4 5) entran máximo 700mA (7 segmentos encendidos a la vez).
