mexomagno/TimerCharlas/Hardware/Componentes/ltSpice/Display 7 segmentos.asc

D1: LED
D2: LED
D3: LED
D4: LED
D5: LED
D6: LED
D7: LED
D8: LED
D9: LED
D10: LED
D11: LED
D12: LED
D13: LED
D14: LED
D15: LED
D16: LED
D17: LED
D18: LED
D19: LED
D20: LED
D21: LED
D22: LED
D23: LED
D24: LED
D25: LED
D26: LED
D27: LED
D28: LED
D29: LED
D30: LED
D31: LED
D32: LED
D33: LED
D34: LED
D35: LED
R1: res; 165; tol=5 pwr=1/4
R2: res; 165; tol=5 pwr=1/4
R3: res; 165; tol=5 pwr=1/4
R4: res; 165; tol=5 pwr=1/4
R5: res; 165; tol=5 pwr=1/4
R6: res; 165; tol=5 pwr=1/4
R7: res; 165; tol=5 pwr=1/4
R8: res; 165; tol=5 pwr=1/4
R9: res; 165; tol=5 pwr=1/4
R10: res; 165; tol=5 pwr=1/4
R11: res; 165; tol=5 pwr=1/4
R12: res; 165; tol=5 pwr=1/4
R13: res; 165; tol=5 pwr=1/4
R14: res; 165; tol=5 pwr=1/4
R15: res; 165; tol=5 pwr=1/4
R16: res; 165; tol=5 pwr=1/4
R17: res; 165; tol=5 pwr=1/4
R18: res; 165; tol=5 pwr=1/4
R19: res; 165; tol=5 pwr=1/4
R20: res; 165; tol=5 pwr=1/4
R21: res; 165; tol=5 pwr=1/4
R22: res; 165; tol=5 pwr=1/4
R23: res; 165; tol=5 pwr=1/4
R24: res; 165; tol=5 pwr=1/4
R25: res; 165; tol=5 pwr=1/4
R26: res; 165; tol=5 pwr=1/4
R27: res; 165; tol=5 pwr=1/4
R28: res; 165; tol=5 pwr=1/4
R29: res; 165; tol=5 pwr=1/4
R30: res; 165; tol=5 pwr=1/4
R31: res; 165; tol=5 pwr=1/4
R32: res; 165; tol=5 pwr=1/4
R33: res; 165; tol=5 pwr=1/4
R34: res; 165; tol=5 pwr=1/4
R35: res; 165; tol=5 pwr=1/4
Named nets: 5V, A, B, C, D, E, F, G
Led ROJO: 1.7v, funciona a 20mA.
Resistencia en serie con cada uno.
Diseñado para funcionar con 5V
(5-1.7)/0.02=165 ohms cada resistencia.
 
Las resistencias reales son de 180 ohms
